TVavrinec/SOC-text/img/orientacni-obrazky/C1, R4.png

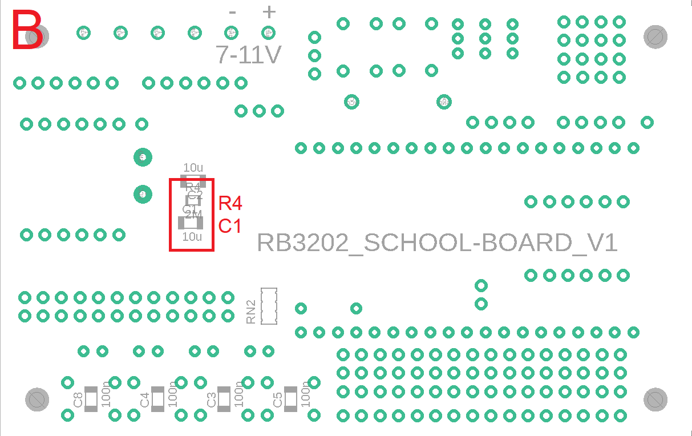
img/orientacni-obrazky/C1, R4.png
