TVavrinec/SOC-text/img/orientacni-obrazky/C3, 4, 5, 8.png

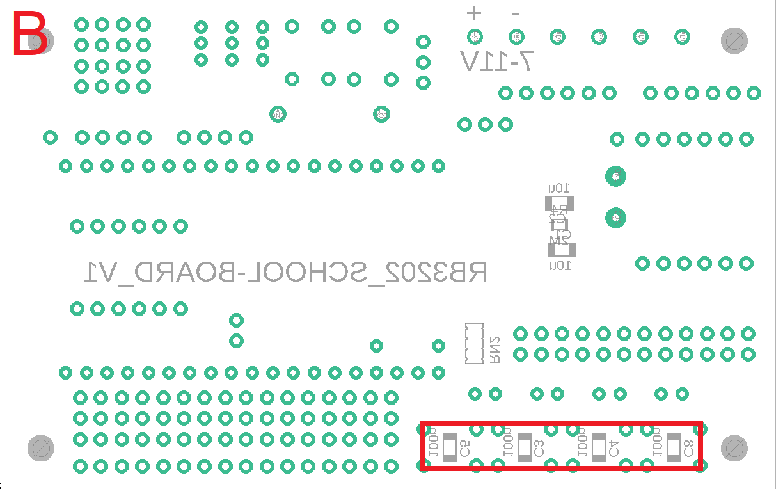
img/orientacni-obrazky/C3, 4, 5, 8.png
