TVavrinec/SOC-text/img/orientacni-obrazky/D2-RN2.png

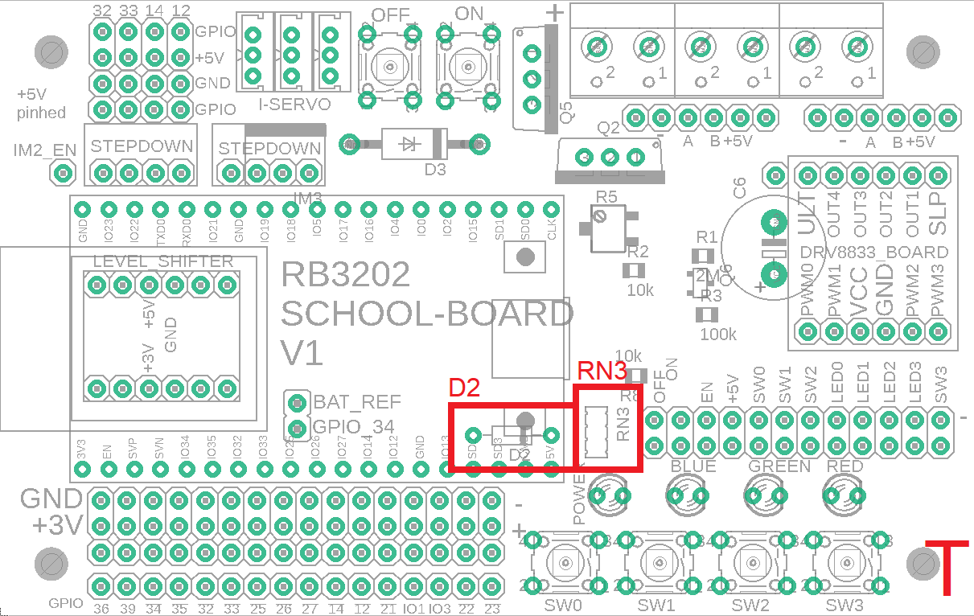
img/orientacni-obrazky/D2-RN2.png
