TVavrinec/SOC-text/img/orientacni-obrazky/devkit.png

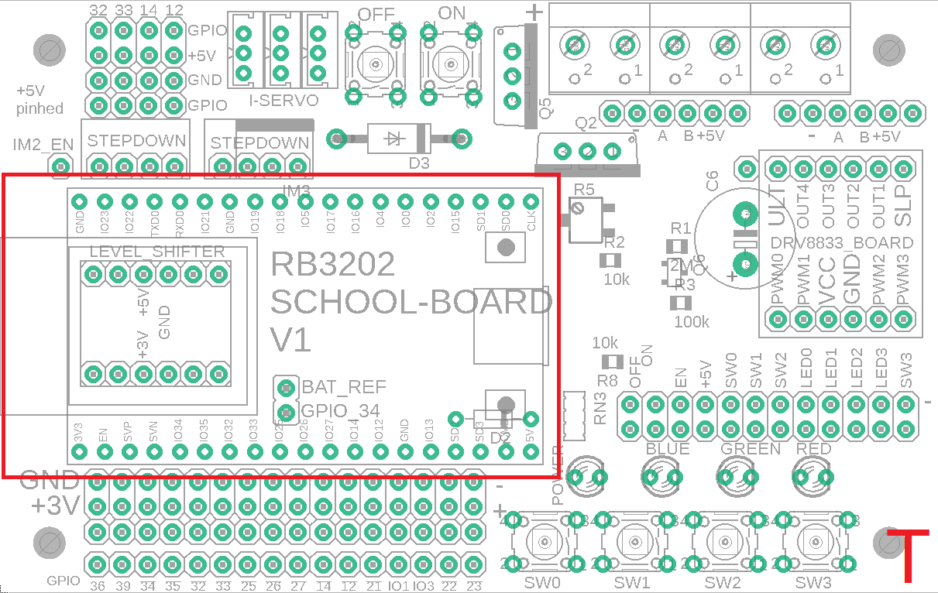
img/orientacni-obrazky/devkit.png
