TVavrinec/SOC-text/img/orientacni-obrazky/IM3, IM4.png

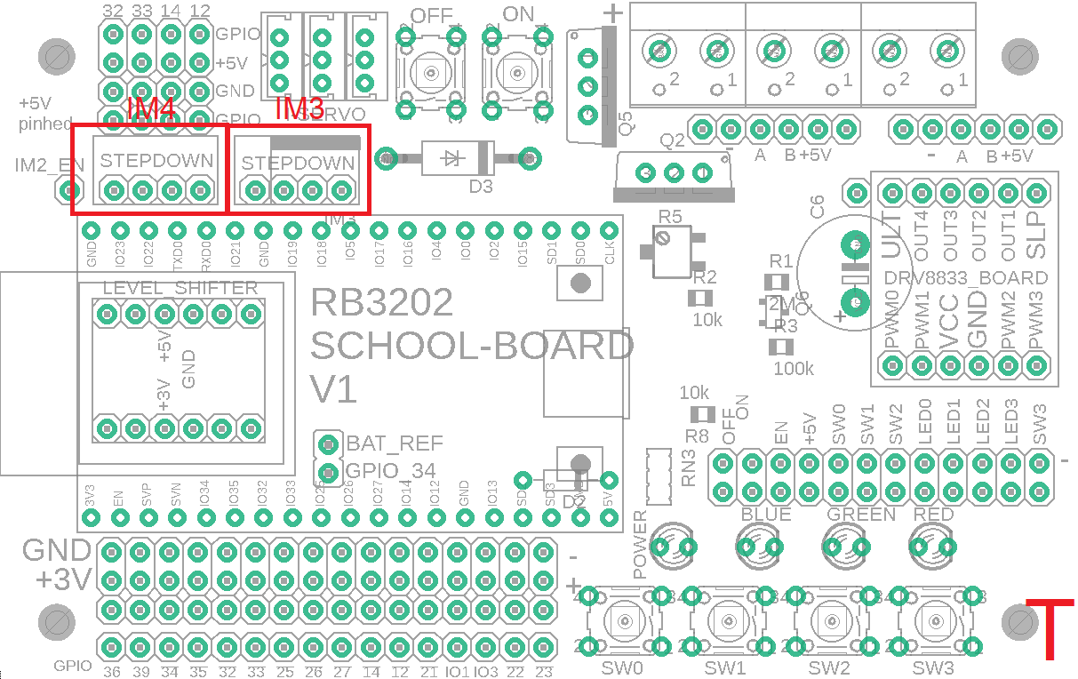
img/orientacni-obrazky/IM3, IM4.png
