TVavrinec/SOC-text/img/orientacni-obrazky/IM10.png

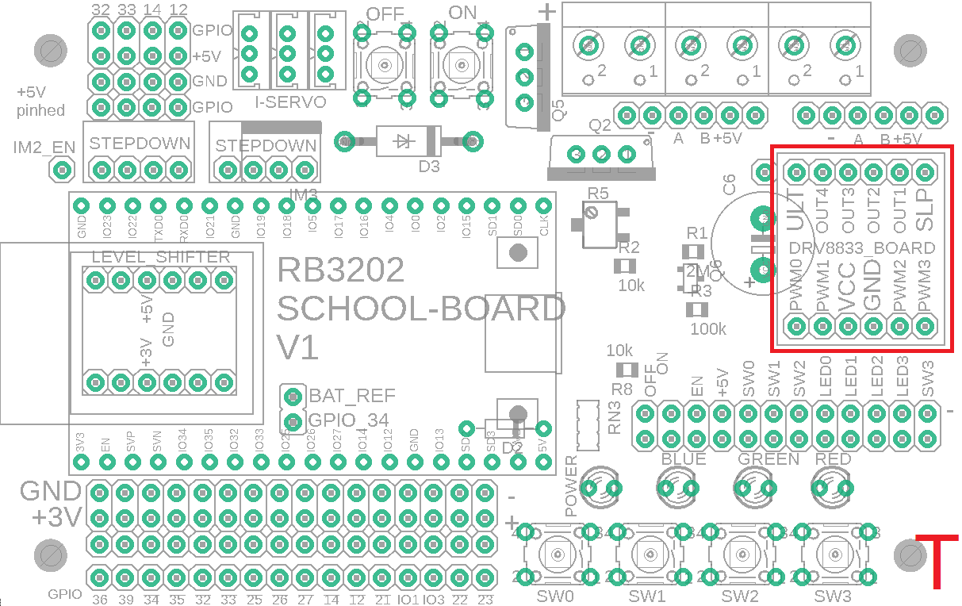
img/orientacni-obrazky/IM10.png
