TVavrinec/SOC-text/img/orientacni-obrazky/JP1, 3, 7.png

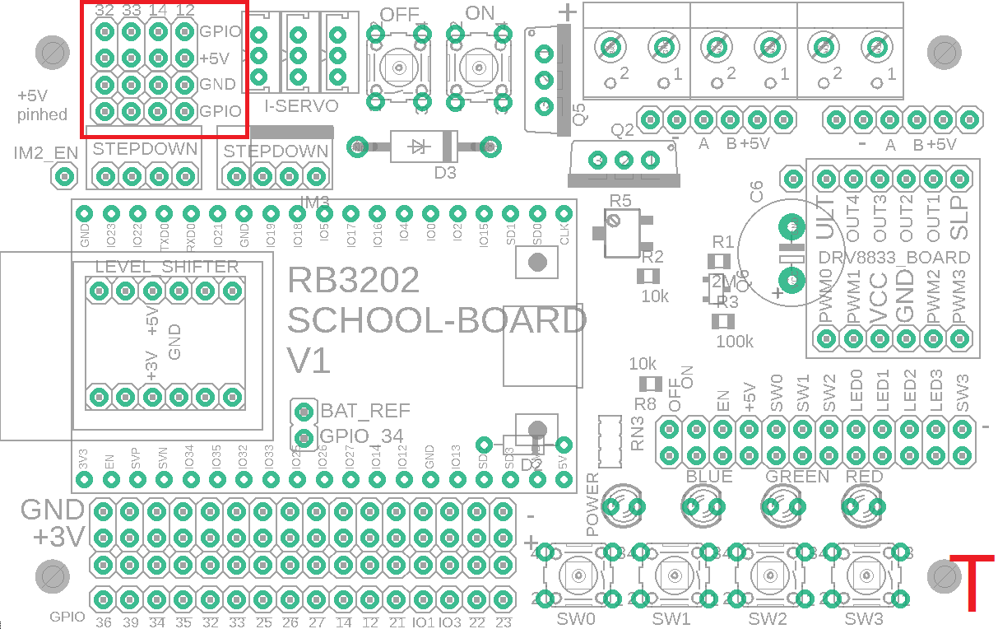
img/orientacni-obrazky/JP1, 3, 7.png
