TVavrinec/SOC-text/img/orientacni-obrazky/JP2.png

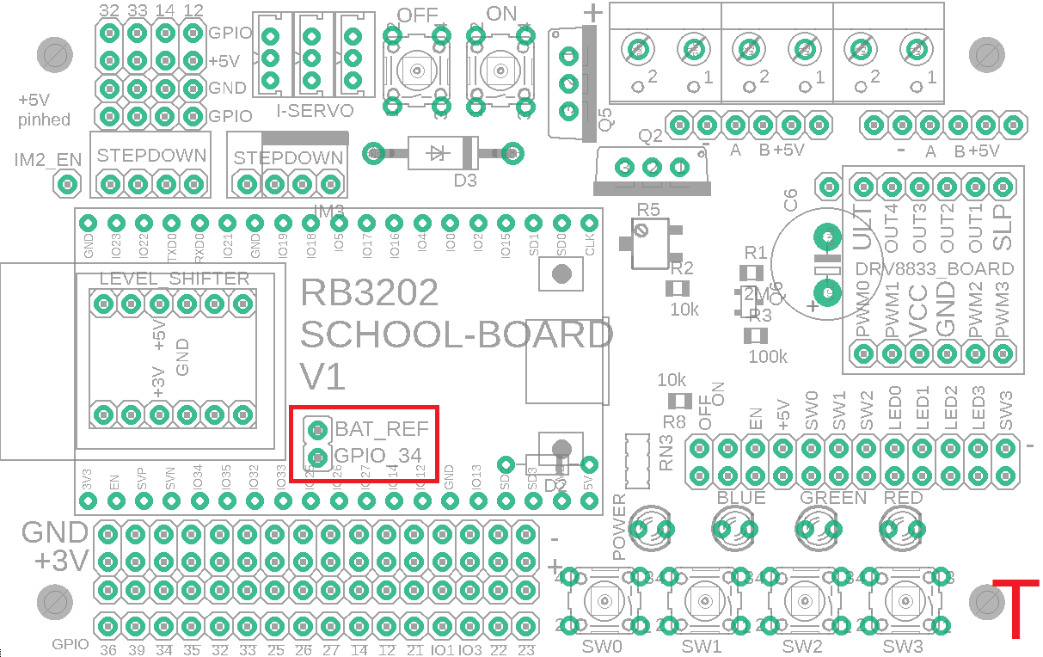
img/orientacni-obrazky/JP2.png
