TVavrinec/SOC-text/img/orientacni-obrazky/JP4,6,9.png

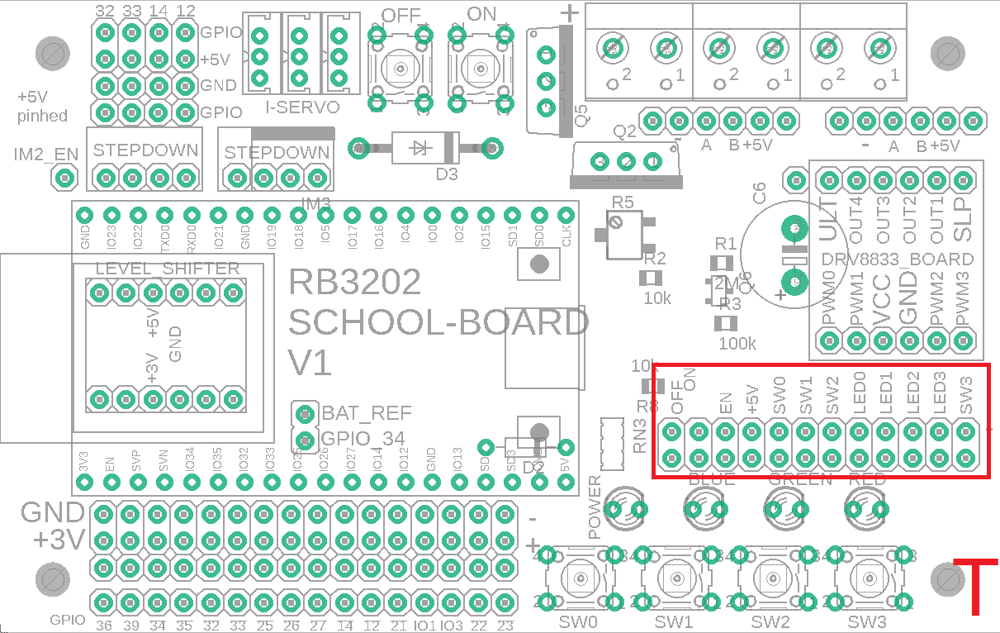
img/orientacni-obrazky/JP4,6,9.png
