TVavrinec/SOC-text/img/orientacni-obrazky/JP5, 8, 11.png

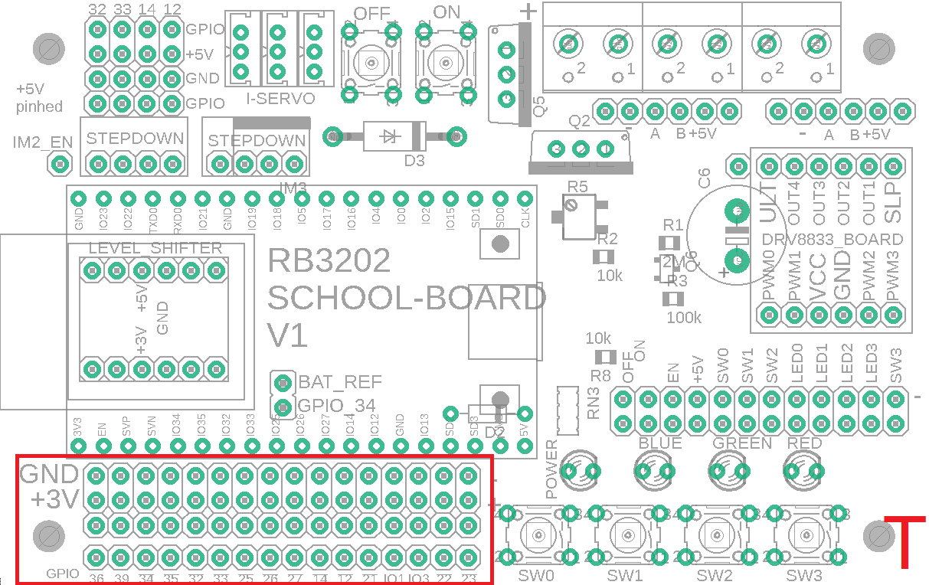
img/orientacni-obrazky/JP5, 8, 11.png
