TVavrinec/SOC-text/img/orientacni-obrazky/JP42, 47, 48, C6, D3.png

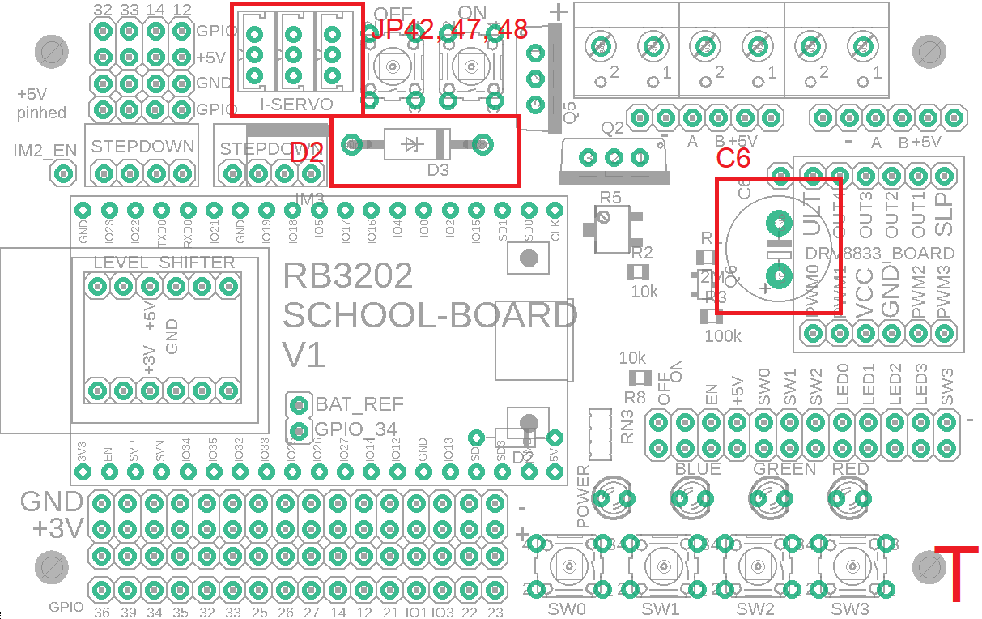
img/orientacni-obrazky/JP42, 47, 48, C6, D3.png
