TVavrinec/SOC-text/img/orientacni-obrazky/ledky.png

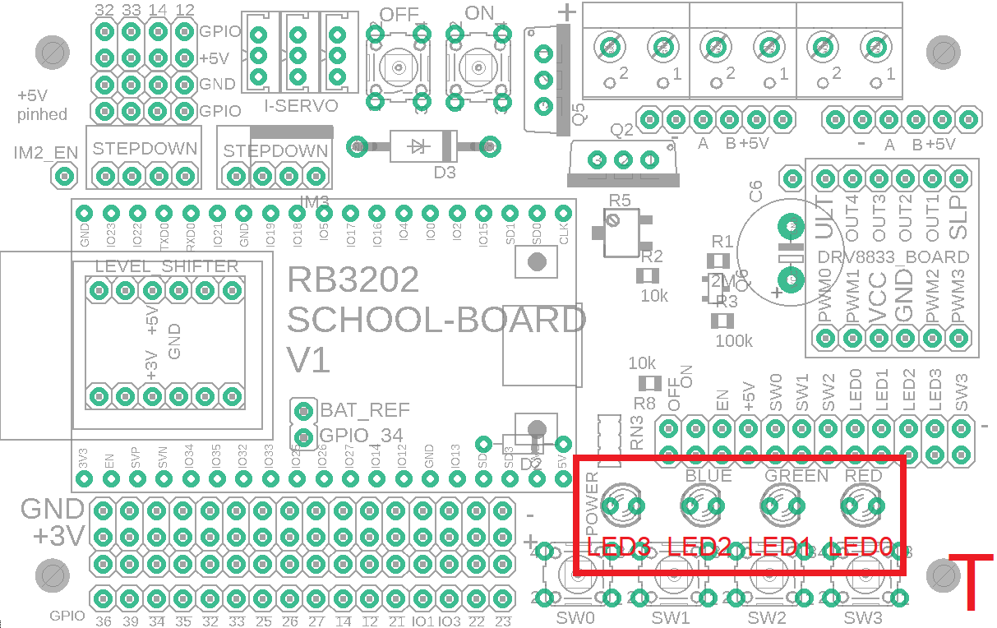
img/orientacni-obrazky/ledky.png
