TVavrinec/SOC-text/img/orientacni-obrazky/level_shifter.png

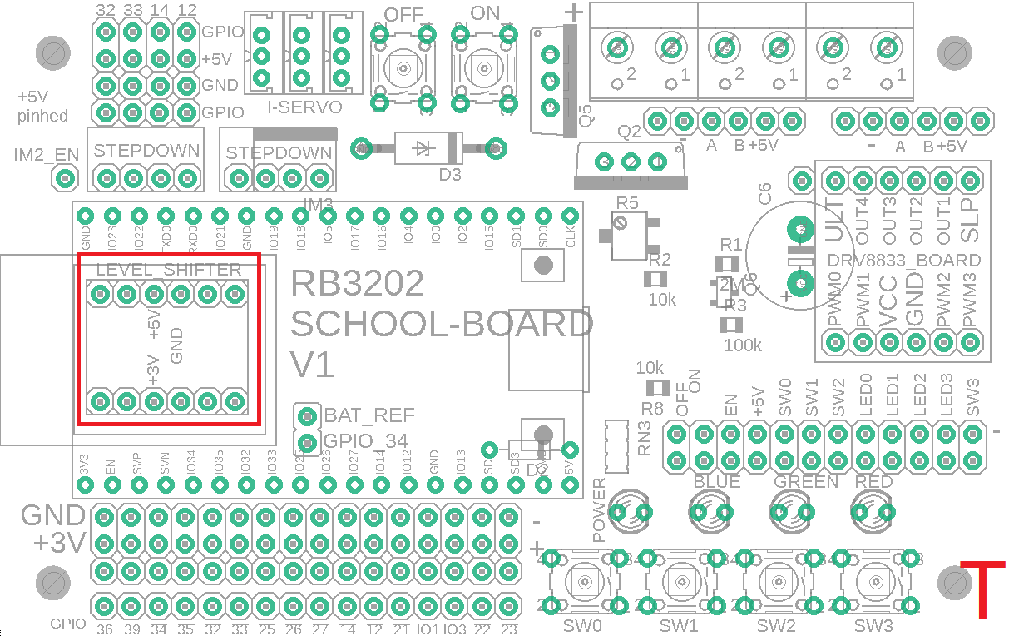
img/orientacni-obrazky/level_shifter.png
