TVavrinec/SOC-text/img/orientacni-obrazky/LP6,12.png

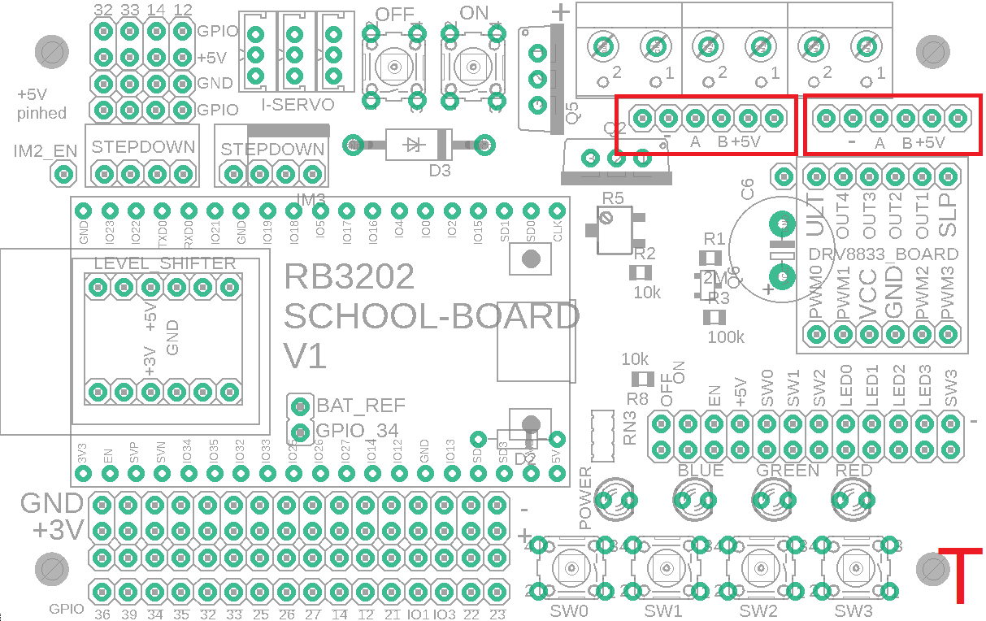
img/orientacni-obrazky/LP6,12.png
