TVavrinec/SOC-text/img/orientacni-obrazky/Q2.png

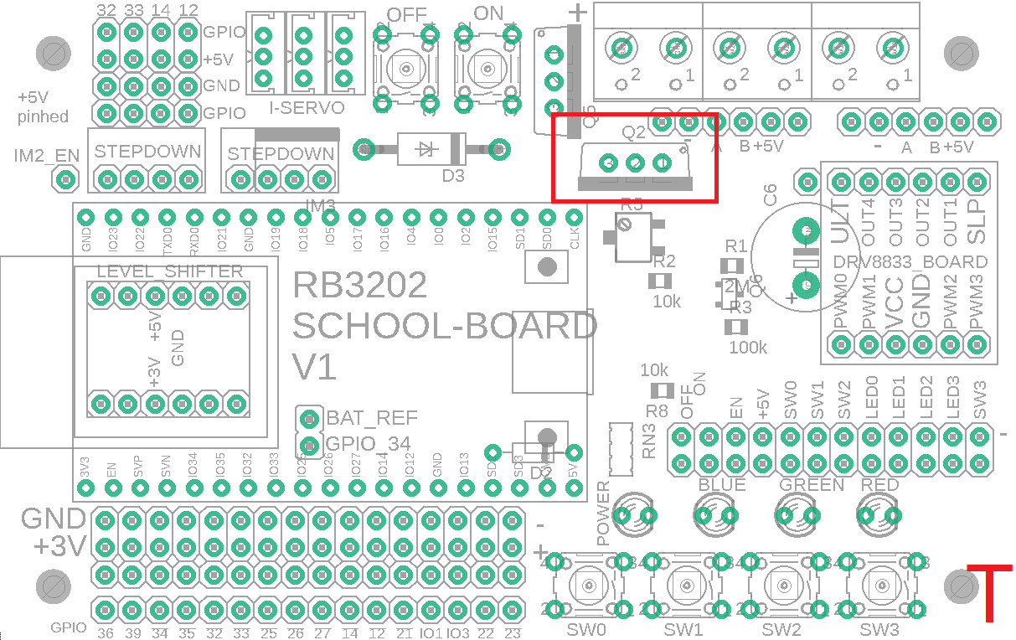
img/orientacni-obrazky/Q2.png
