TVavrinec/SOC-text/img/orientacni-obrazky/Q5.png

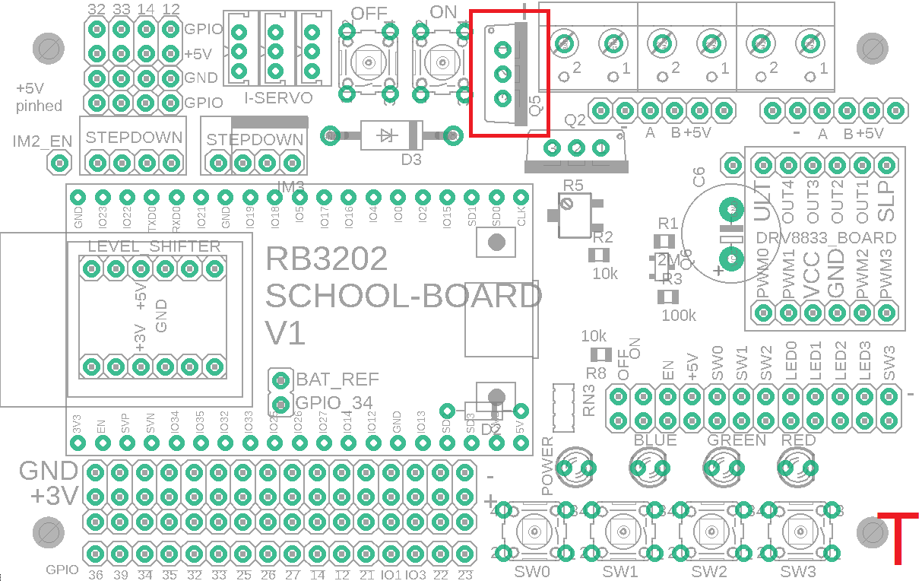
img/orientacni-obrazky/Q5.png
