TVavrinec/SOC-text/img/orientacni-obrazky/R3, Q6.png

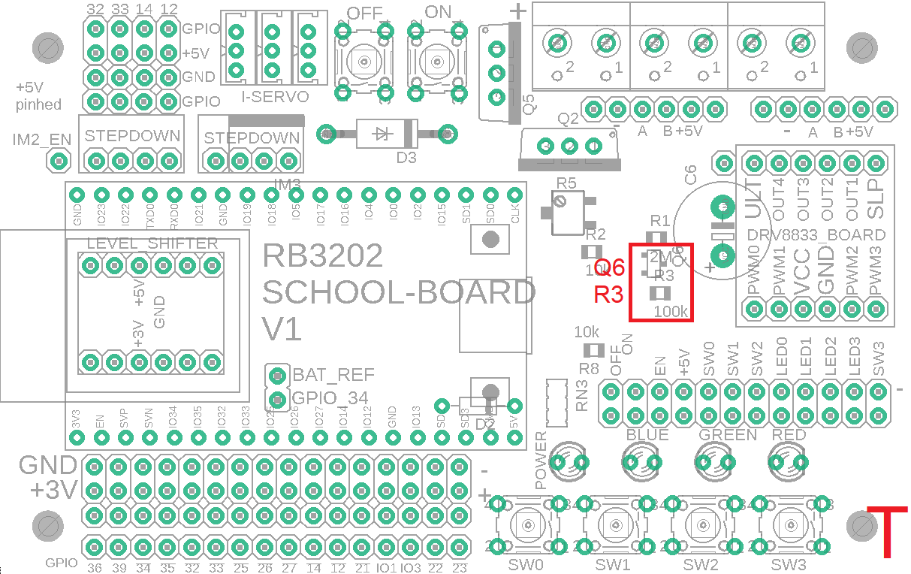
img/orientacni-obrazky/R3, Q6.png
