TVavrinec/SOC-text/img/orientacni-obrazky/RN2.png

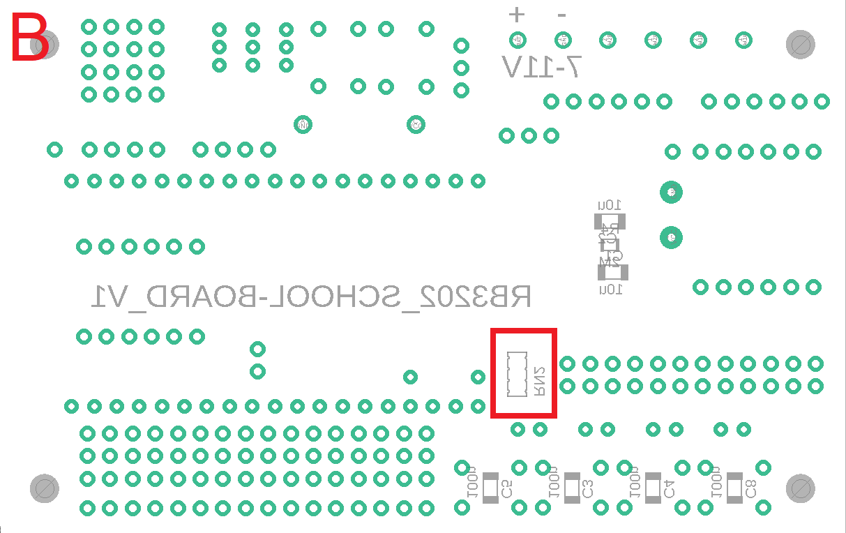
img/orientacni-obrazky/RN2.png
