TVavrinec/SOC-text/img/orientacni-obrazky/SW5, SW1.png

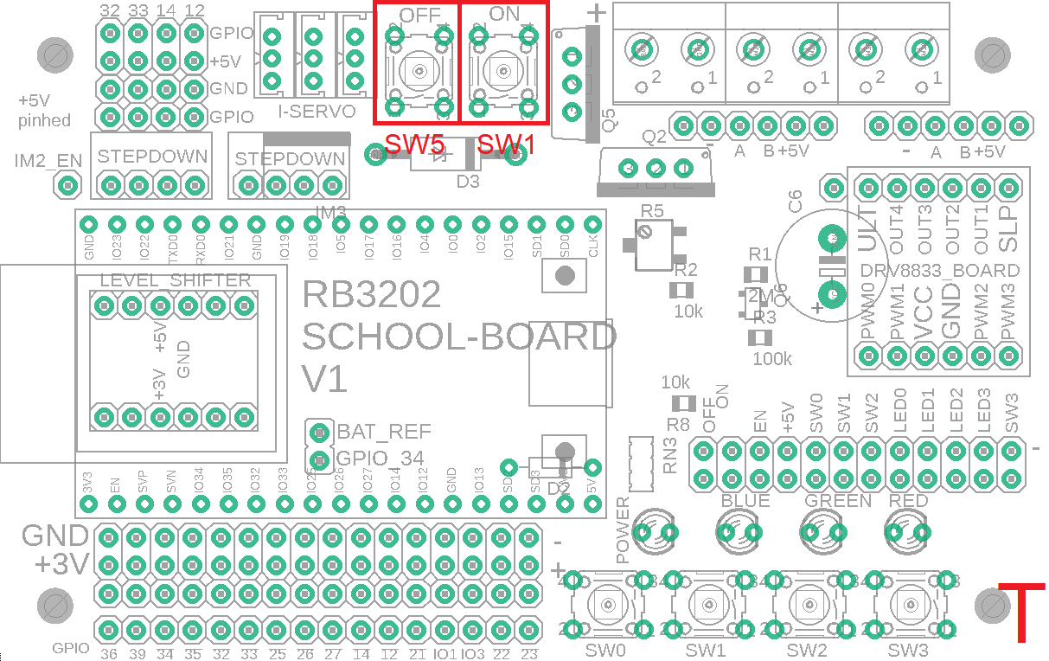
img/orientacni-obrazky/SW5, SW1.png
