TVavrinec/SOC-text/img/orientacni-obrazky/SW-0-3.png

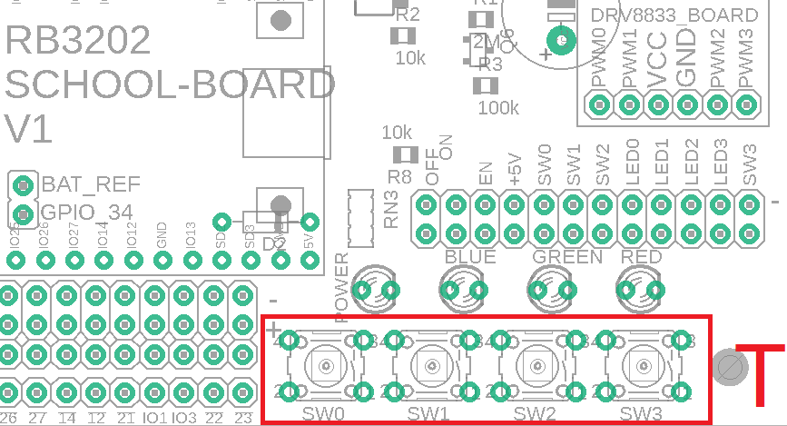
img/orientacni-obrazky/SW-0-3.png
