TVavrinec/SOC-text/img/rizeni drd8833.png

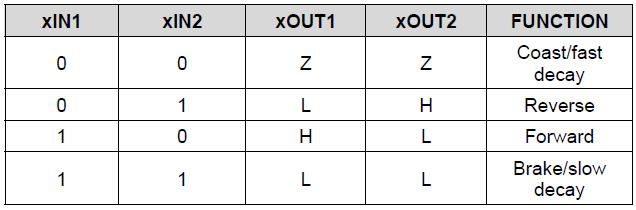
img/rizeni drd8833.png
