TVavrinec/SOC-text/img/sada1.JPG

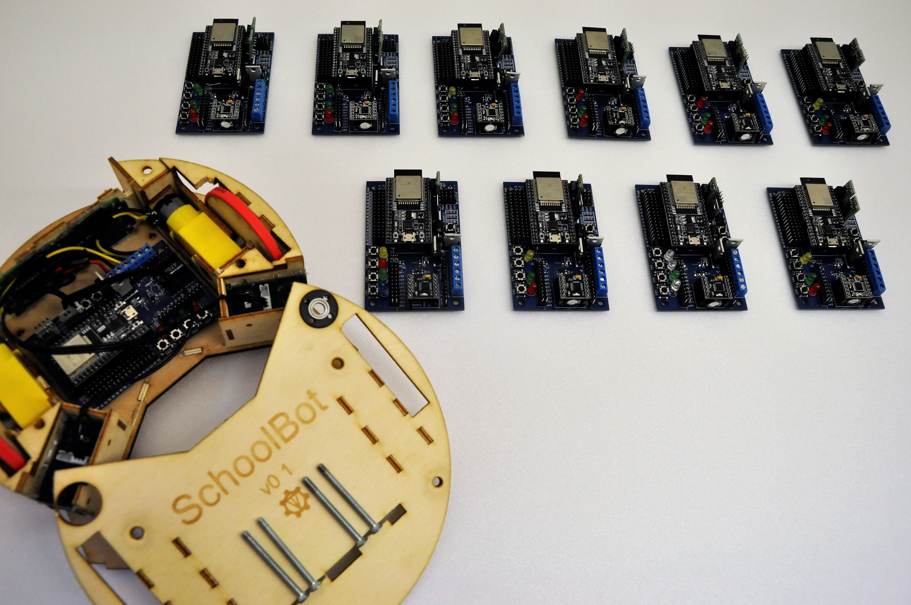
img/sada1.JPG
