TVavrinec/SOC-text/template/header.png

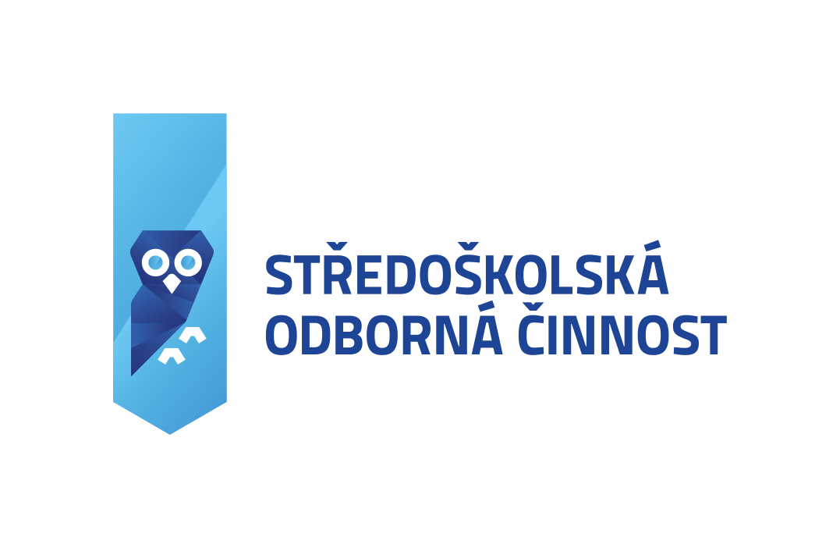
template/header.png
