TVavrinec/SOC-text/template/jcmm.png

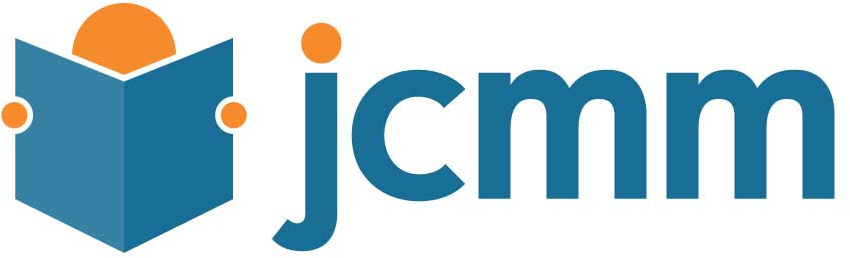
template/jcmm.png
