TVavrinec/SOC-text/template/jmk.png

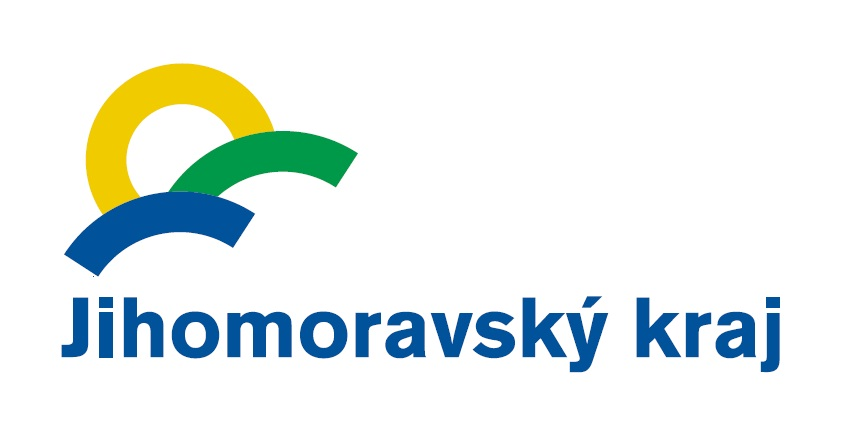
template/jmk.png
